Rose-Hulman-ROBO4xx/1314-BeagleBone-Quadcopter/code/ControlTower/images/BBB.jpg

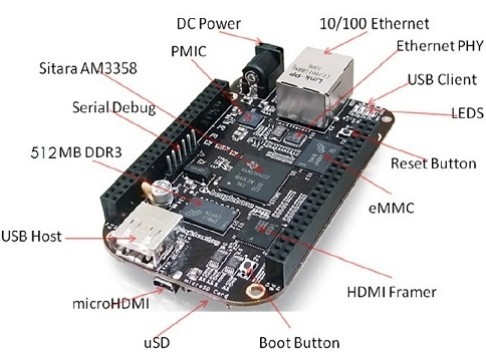
code/ControlTower/images/BBB.jpg
