Rose-Hulman-ROBO4xx/1314-BeagleBone-Quadcopter/code/ControlTower/images/Camera.jpg

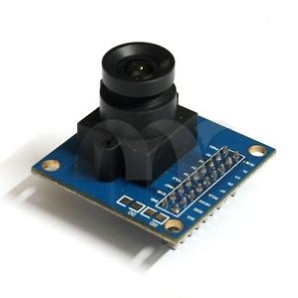
code/ControlTower/images/Camera.jpg
