Rose-Hulman-ROBO4xx/1314-BeagleBone-Quadcopter/code/ControlTower/images/Cape.jpg

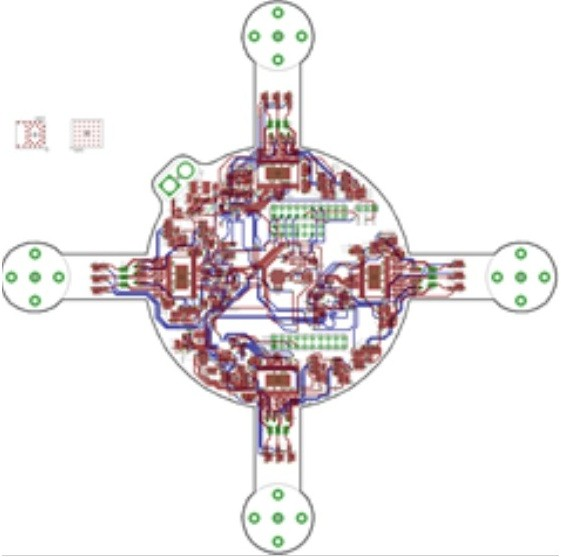
code/ControlTower/images/Cape.jpg
