Rose-Hulman-ROBO4xx/1314-BeagleBone-Quadcopter/code/ControlTower/images/forward_0.gif

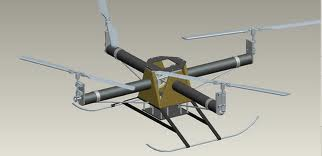
code/ControlTower/images/forward_0.gif
