Rose-Hulman-ROBO4xx/1314-BeagleBone-Quadcopter/code/ControlTower/images/forward_-1.gif

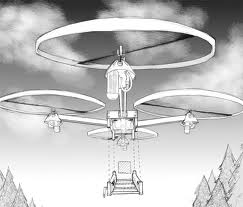
code/ControlTower/images/forward_-1.gif
