Rose-Hulman-ROBO4xx/1314-BeagleBone-Quadcopter/code/ControlTower/images/MPU.jpg

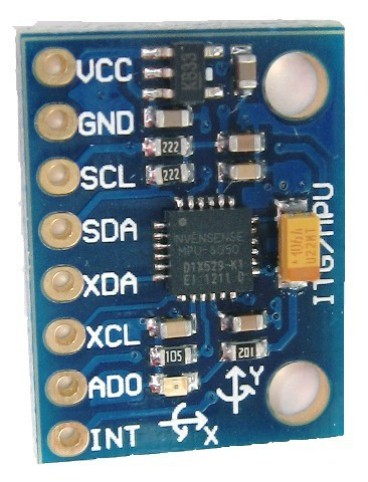
code/ControlTower/images/MPU.jpg
