Rose-Hulman-ROBO4xx/1314-BeagleBone-Quadcopter/code/ControlTower/images/original.gif

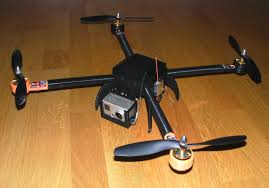
code/ControlTower/images/original.gif
