Rose-Hulman-ROBO4xx/1314-BeagleBone-Quadcopter/code/ControlTower/images/original.jpg

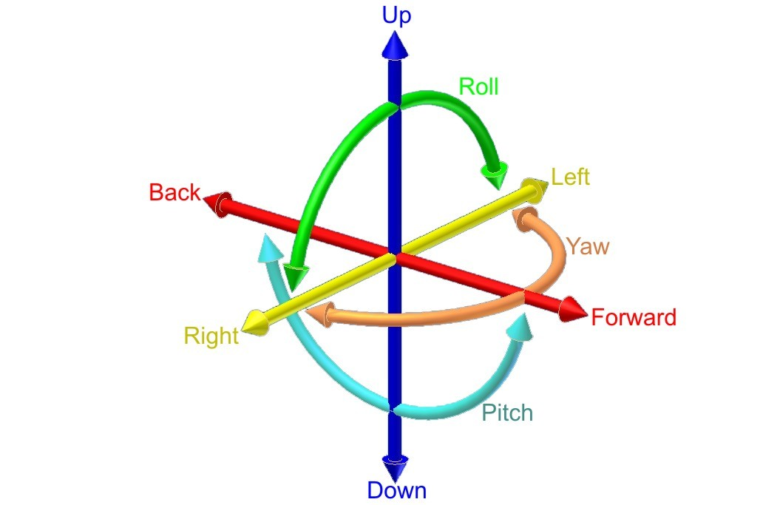
code/ControlTower/images/original.jpg
