Rose-Hulman-ROBO4xx/1314-BeagleBone-Quadcopter/code/ControlTower/images/QuadCopterImage.jpg

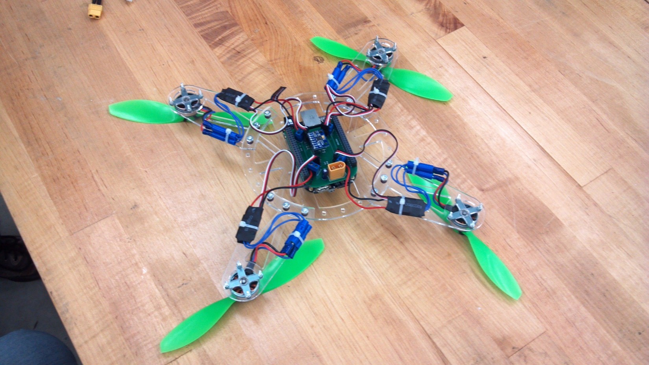
code/ControlTower/images/QuadCopterImage.jpg
