Rose-Hulman-ROBO4xx/1314-BeagleBone-Quadcopter/code/ControlTower/images/TIDog.png

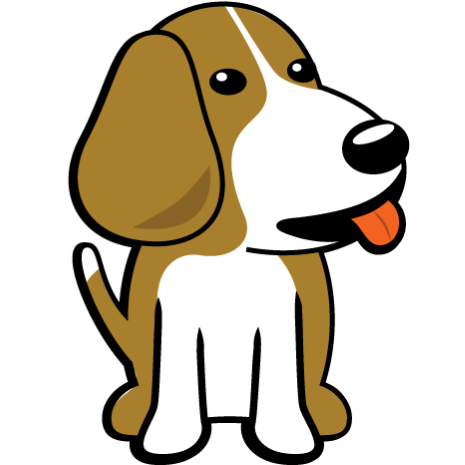
code/ControlTower/images/TIDog.png
