Rose-Hulman-ROBO4xx/1314-BeagleBone-Quadcopter/code/ControlTower/images/UltraSonic.jpg

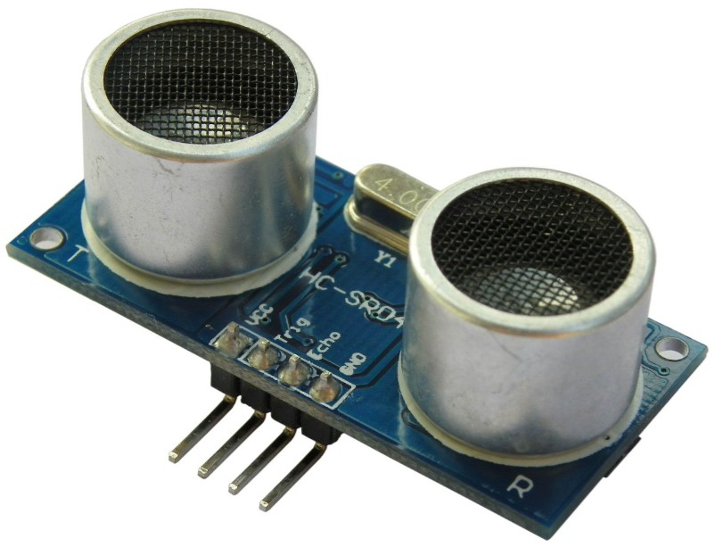
code/ControlTower/images/UltraSonic.jpg
