Rose-Hulman-ROBO4xx/1314-BeagleBone-Quadcopter/noncode/Board/Quad1brd.png

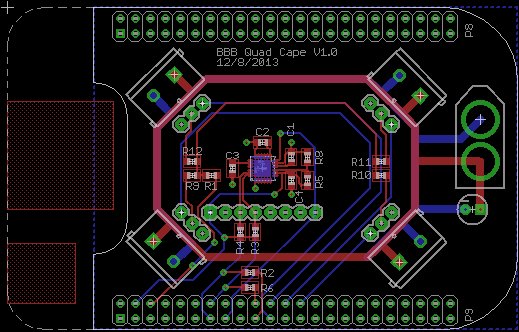
noncode/Board/Quad1brd.png
