Rose-Hulman-ROBO4xx/1314-BeagleBone-Quadcopter/noncode/Board/Quad2brd.png

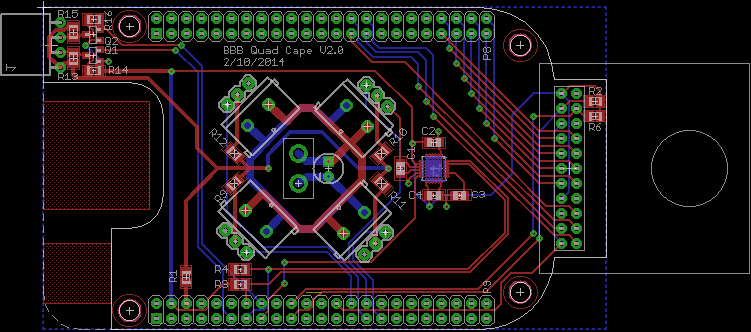
noncode/Board/Quad2brd.png
