Rose-Hulman-ROBO4xx/1314-BeagleBone-Quadcopter/noncode/Board/Quad3brd.png

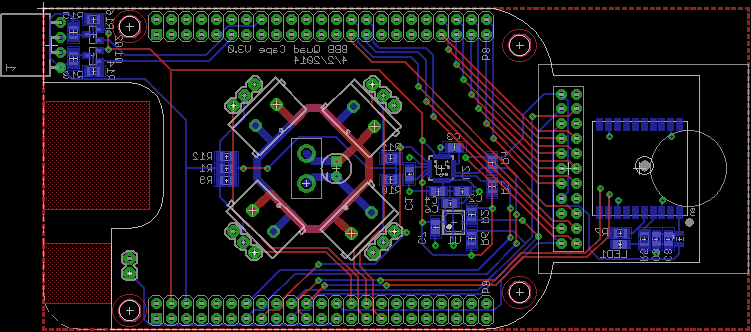
noncode/Board/Quad3brd.png
