Rose-Hulman-ROBO4xx/1314-BeagleBone-Quadcopter/noncode/Board/Quad32brd.png

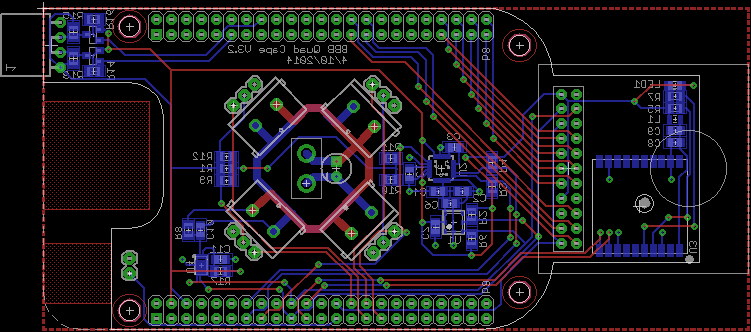
noncode/Board/Quad32brd.png
