Rose-Hulman-ROBO4xx/1314-BeagleBone-Quadcopter/noncode/Pictures/2013-12-18_14-34-24_871.jpg

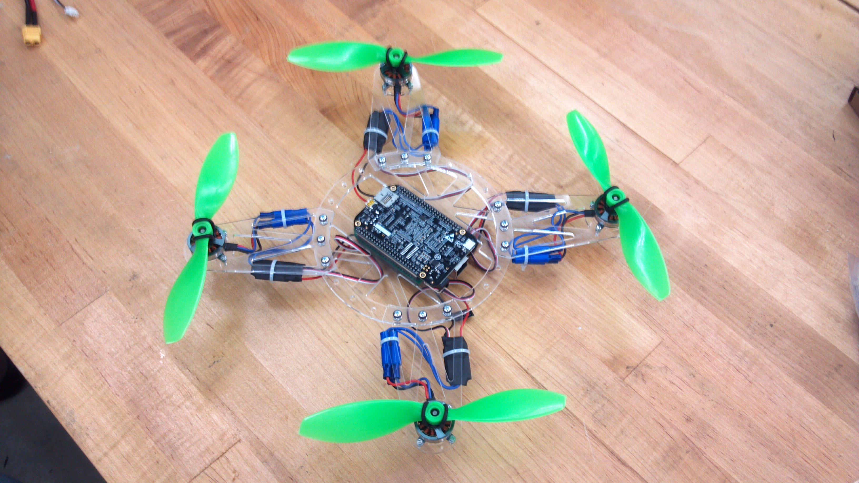
noncode/Pictures/2013-12-18_14-34-24_871.jpg
