Rose-Hulman-ROBO4xx/1314-BeagleBone-Quadcopter/noncode/CAD/Battery Tray 4.0 plywood tabbed.dxf

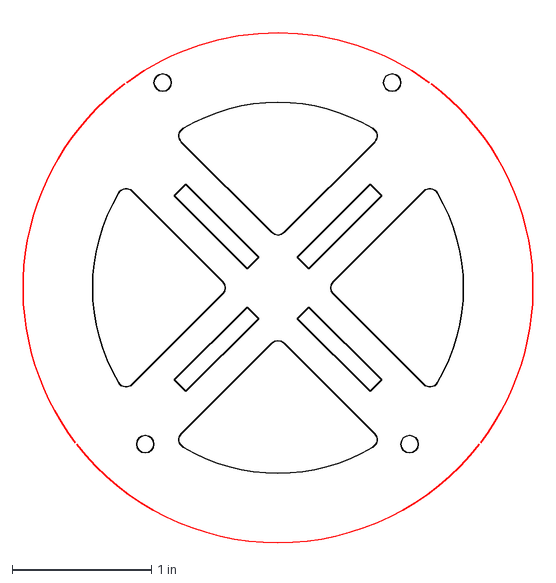
[picture p55: CAD file, 2014-04-13]
noncode/CAD/Battery Tray 4.0 plywood tabbed.dxf
3.77 x 3.79 in
