Rose-Hulman-ROBO4xx/1314-BeagleBone-Quadcopter/noncode/CAD/Layout 12x24 Plywood 4-7-14.dxf

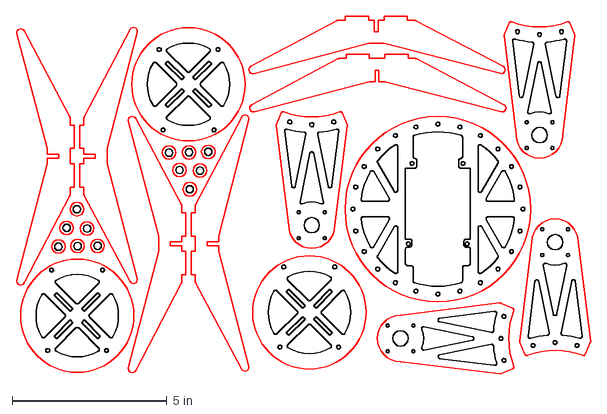
[picture p56: CAD file, 2014-04-13]
noncode/CAD/Layout 12x24 Plywood 4-7-14.dxf
18.6 x 11.6 in
