Rose-Hulman-ROBO4xx/1314-BeagleBone-Quadcopter/noncode/CAD/ESC.SLDPRT

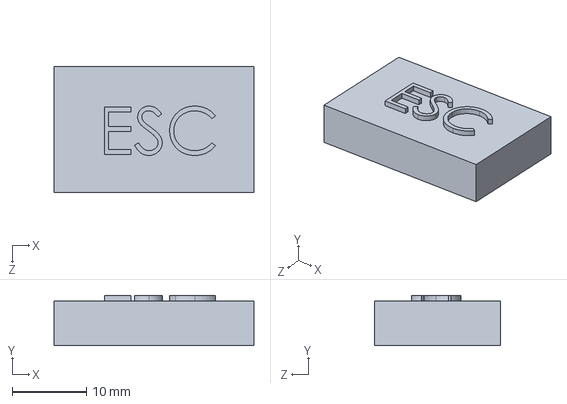
[picture p57: CAD file, 2014-04-13]
noncode/CAD/ESC.SLDPRT
27.0 x 6.76 x 17.0 mm
