Rose-Hulman-ROBO4xx/1314-BeagleBone-Quadcopter/noncode/CAD/Layout 12x12 with Grain.dxf

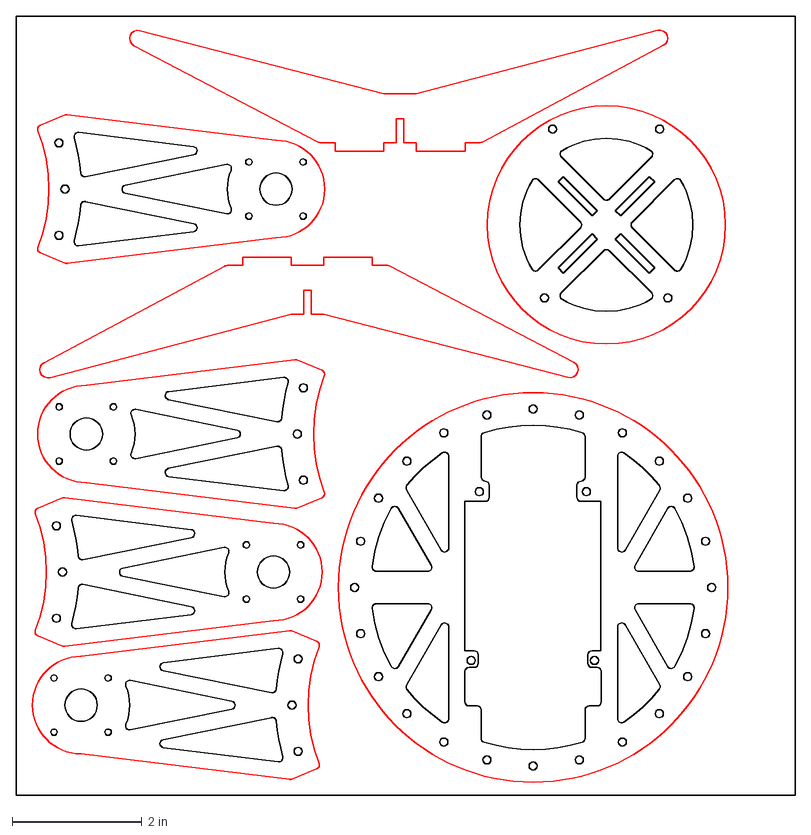
[picture p59: CAD file, 2014-04-13]
noncode/CAD/Layout 12x12 with Grain.dxf
12.0 x 12.0 in
