Rose-Hulman-ROBO4xx/1314-BeagleBone-Quadcopter/noncode/CAD/Battery Tray 4.0 plywood.dxf

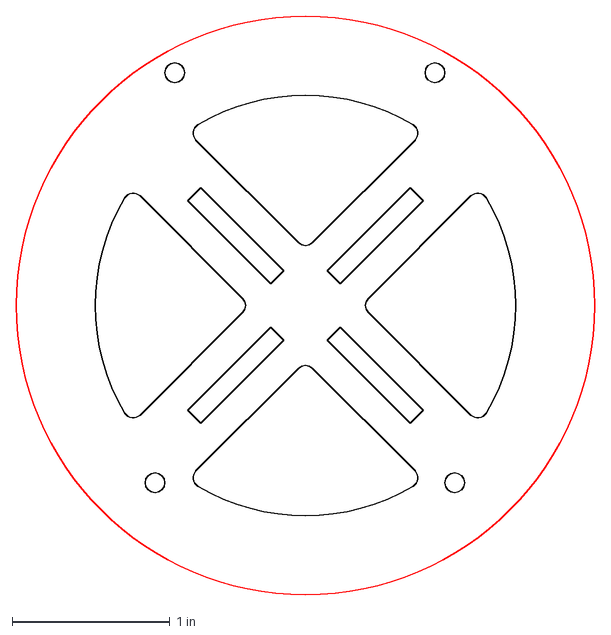
[picture p60: CAD file, 2014-04-13]
noncode/CAD/Battery Tray 4.0 plywood.dxf
3.67 x 3.67 in
