Rose-Hulman-ROBO4xx/1314-BeagleBone-Quadcopter/noncode/CAD/Battery Tray 4.0.SLDPRT

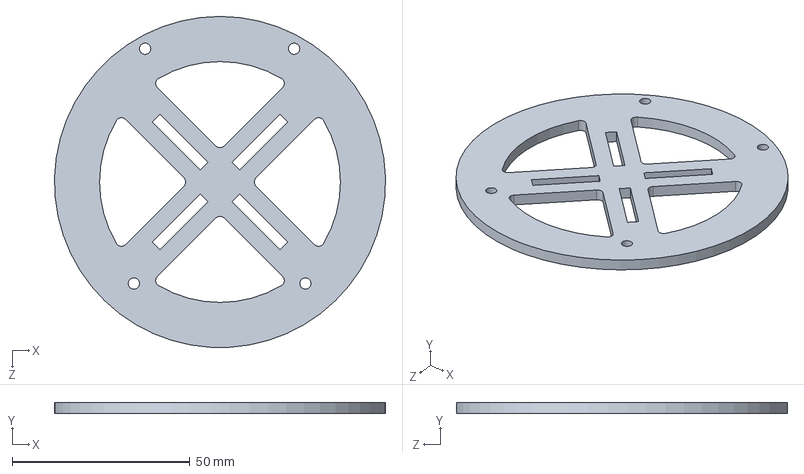
[picture p61: CAD file, 2014-04-13]
noncode/CAD/Battery Tray 4.0.SLDPRT
93.1 x 3.17 x 93.2 mm
