Rose-Hulman-ROBO4xx/1314-BeagleBone-Quadcopter/noncode/CAD/Arm 4.0.SLDPRT

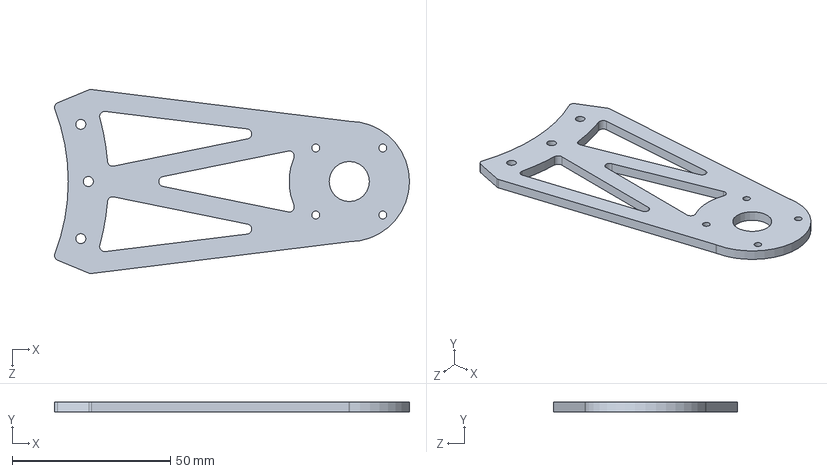
[picture p62: CAD file, 2014-04-13]
noncode/CAD/Arm 4.0.SLDPRT
112.3 x 3.17 x 58.2 mm
