Rose-Hulman-ROBO4xx/1314-BeagleBone-Quadcopter/noncode/CAD/Propellor.SLDPRT

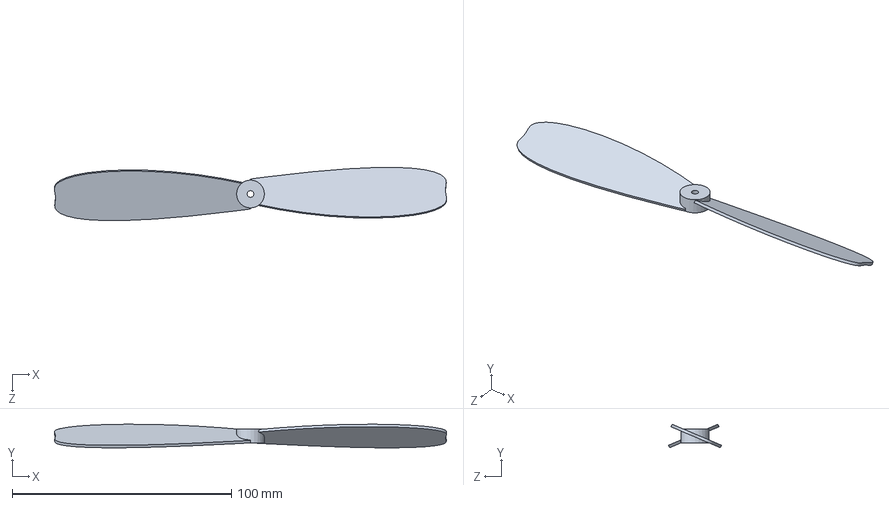
[picture p63: CAD file, 2014-04-13]
noncode/CAD/Propellor.SLDPRT
178.8 x 10.8 x 24.2 mm
