Rose-Hulman-ROBO4xx/1314-BeagleBone-Quadcopter/noncode/CAD/Leg2 4.0 solid plywood.dxf

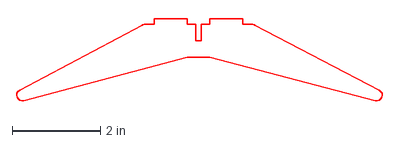
[picture p64: CAD file, 2014-04-13]
noncode/CAD/Leg2 4.0 solid plywood.dxf
8.32 x 1.87 in
