Rose-Hulman-ROBO4xx/1314-BeagleBone-Quadcopter/noncode/CAD/Frame 4.0.SLDPRT

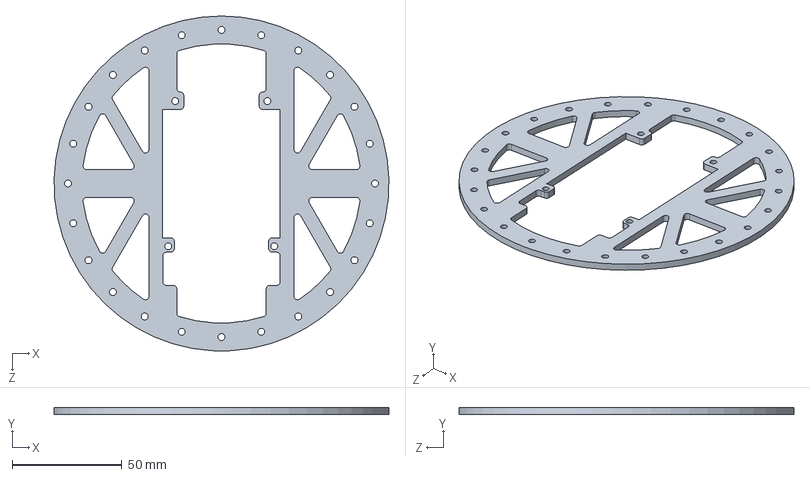
[picture p65: CAD file, 2014-04-13]
noncode/CAD/Frame 4.0.SLDPRT
152.3 x 3.17 x 152.4 mm
