Rose-Hulman-ROBO4xx/1314-BeagleBone-Quadcopter/noncode/CAD/Leg1 4.0 solid plywood.dxf

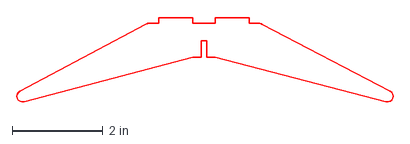
[picture p66: CAD file, 2014-04-13]
noncode/CAD/Leg1 4.0 solid plywood.dxf
8.32 x 1.87 in
