Rose-Hulman-ROBO4xx/1314-BeagleBone-Quadcopter/noncode/CAD/Leg2 4.0 solid plywood tabbed.dxf

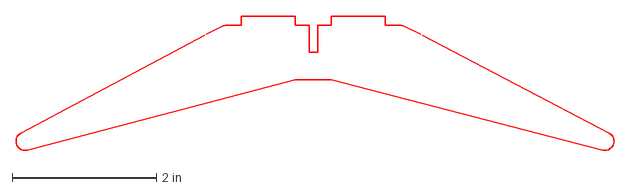
[picture p67: CAD file, 2014-04-13]
noncode/CAD/Leg2 4.0 solid plywood tabbed.dxf
8.29 x 1.87 in
