Rose-Hulman-ROBO4xx/1314-BeagleBone-Quadcopter/noncode/CAD/Prototype 3.SLDPRT

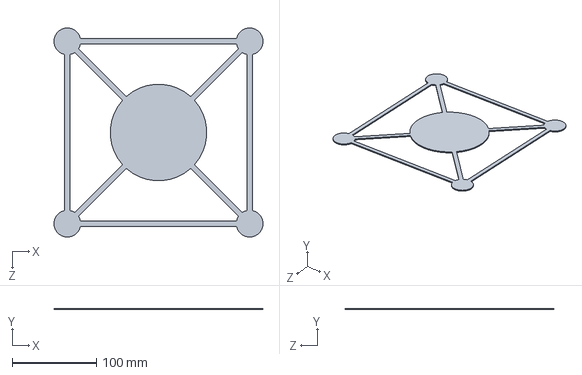
[picture p68: CAD file, 2014-04-08]
noncode/CAD/Prototype 3.SLDPRT
247.5 x 1.57 x 247.5 mm
