Rose-Hulman-ROBO4xx/1314-BeagleBone-Quadcopter/noncode/CAD/Battery 1.0.SLDPRT

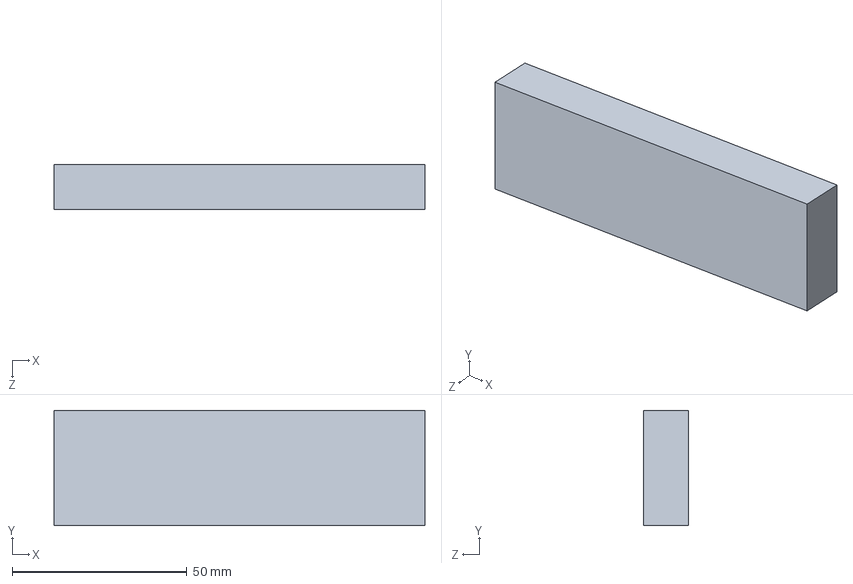
[picture p69: CAD file, 2014-04-08]
noncode/CAD/Battery 1.0.SLDPRT
106.0 x 33.0 x 13.0 mm
