Rose-Hulman-ROBO4xx/1314-BeagleBone-Quadcopter/noncode/CAD/Frame 1.0.SLDPRT

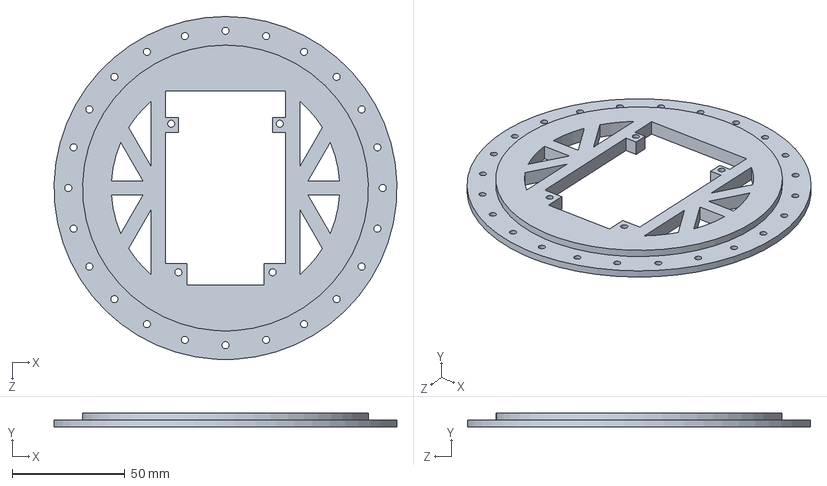
[picture p71: CAD file, 2014-04-08]
noncode/CAD/Frame 1.0.SLDPRT
152.3 x 6.35 x 152.4 mm
