Rose-Hulman-ROBO4xx/1314-BeagleBone-Quadcopter/noncode/CAD/Arm 2.0.SLDPRT

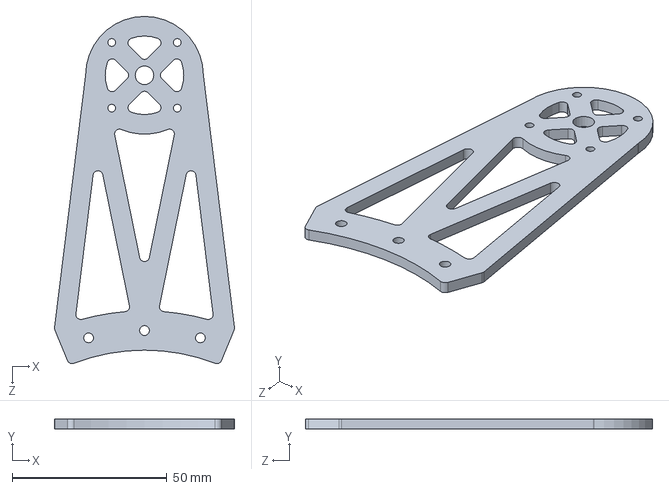
[picture p72: CAD file, 2014-04-08]
noncode/CAD/Arm 2.0.SLDPRT
58.2 x 3.17 x 112.3 mm
