Rose-Hulman-ROBO4xx/1314-BeagleBone-Quadcopter/noncode/CAD/Battery Tray 1.0.SLDPRT

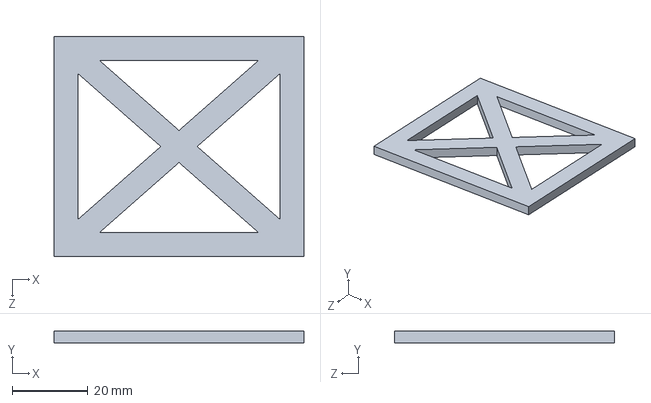
[picture p73: CAD file, 2014-04-08]
noncode/CAD/Battery Tray 1.0.SLDPRT
66.0 x 3.17 x 58.1 mm
