Rose-Hulman-ROBO4xx/1314-BeagleBone-Quadcopter/noncode/CAD/Leg2 2.0.SLDPRT

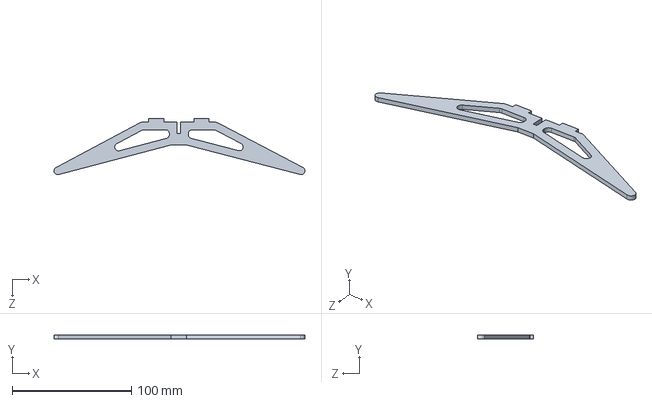
[picture p75: CAD file, 2014-04-08]
noncode/CAD/Leg2 2.0.SLDPRT
210.5 x 3.17 x 47.2 mm
