Rose-Hulman-ROBO4xx/1314-BeagleBone-Quadcopter/noncode/CAD/Leg2 1.0.SLDPRT

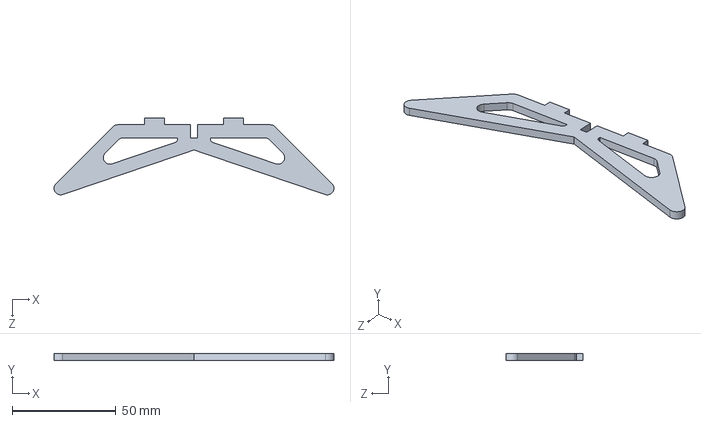
[picture p76: CAD file, 2014-04-08]
noncode/CAD/Leg2 1.0.SLDPRT
134.8 x 3.17 x 37.0 mm
