Rose-Hulman-ROBO4xx/1314-BeagleBone-Quadcopter/noncode/CAD/Layout LegSpacer 4-7-14.dxf

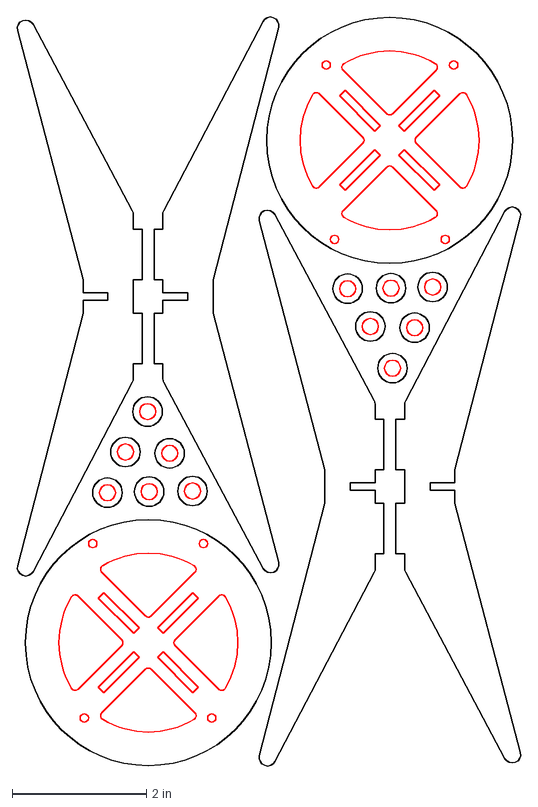
[picture p77: CAD file, 2014-04-08]
noncode/CAD/Layout LegSpacer 4-7-14.dxf
7.53 x 11.2 in
