Rose-Hulman-ROBO4xx/1314-BeagleBone-Quadcopter/noncode/CAD/Arm 1.0.SLDPRT

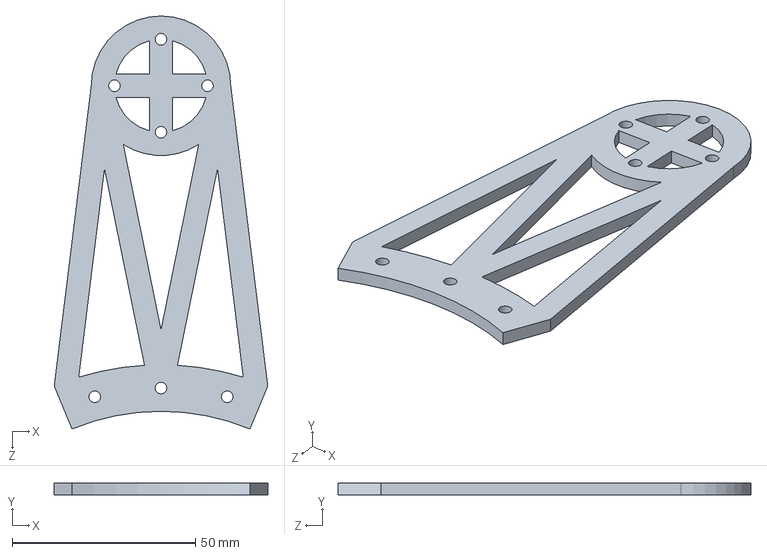
[picture p79: CAD file, 2014-04-08]
noncode/CAD/Arm 1.0.SLDPRT
58.3 x 3.17 x 112.8 mm
