Rose-Hulman-ROBO4xx/1314-BeagleBone-Quadcopter/noncode/CAD/Layout 12x12.dxf

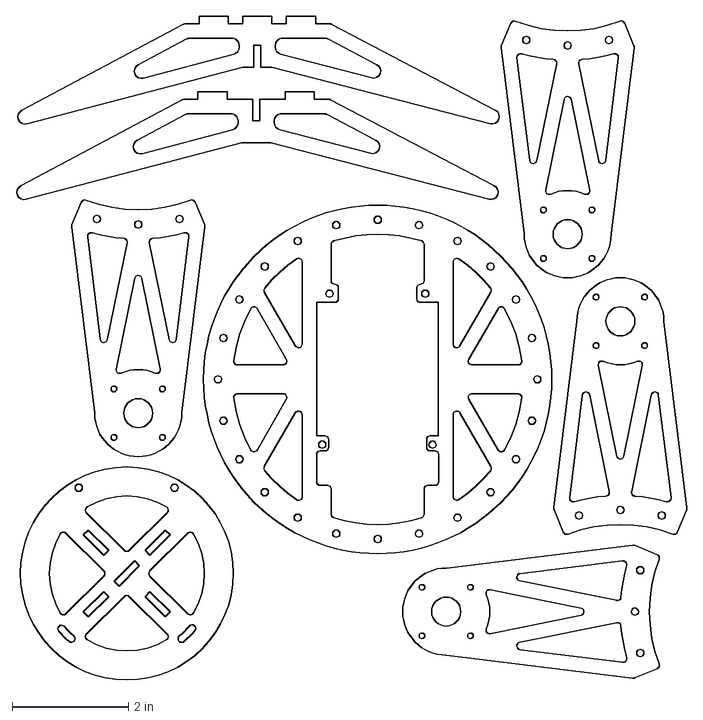
[picture p80: CAD file, 2014-04-08]
noncode/CAD/Layout 12x12.dxf
11.6 x 11.4 in
