Rose-Hulman-ROBO4xx/1314-BeagleBone-Quadcopter/noncode/CAD/Leg2 4.0 solid.dxf

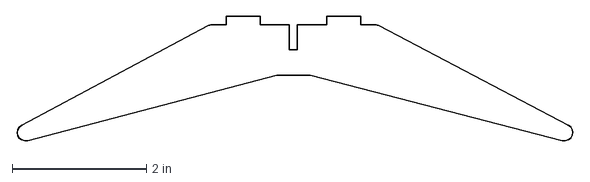
[picture p81: CAD file, 2014-04-08]
noncode/CAD/Leg2 4.0 solid.dxf
8.32 x 1.87 in
