Rose-Hulman-ROBO4xx/1314-BeagleBone-Quadcopter/noncode/CAD/Battery Tray 1.5.SLDPRT

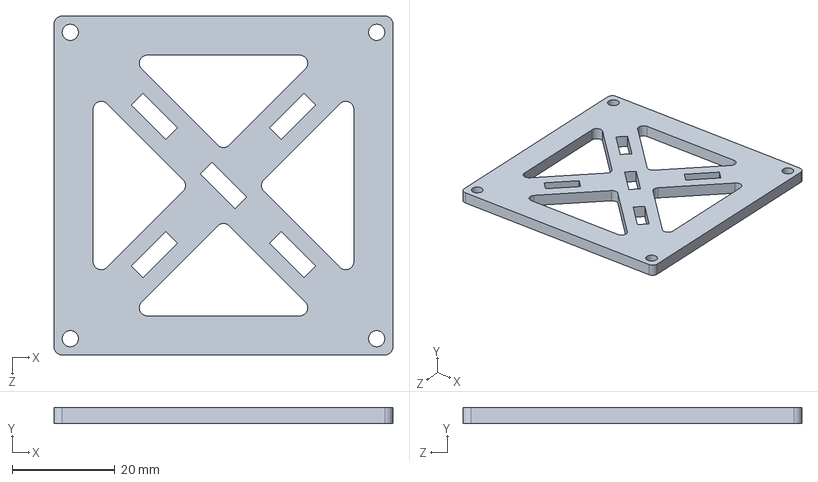
[picture p82: CAD file, 2014-04-08]
noncode/CAD/Battery Tray 1.5.SLDPRT
66.0 x 3.17 x 66.0 mm
