Rose-Hulman-ROBO4xx/1314-BeagleBone-Quadcopter/noncode/CAD/Standoff 1.0.SLDPRT

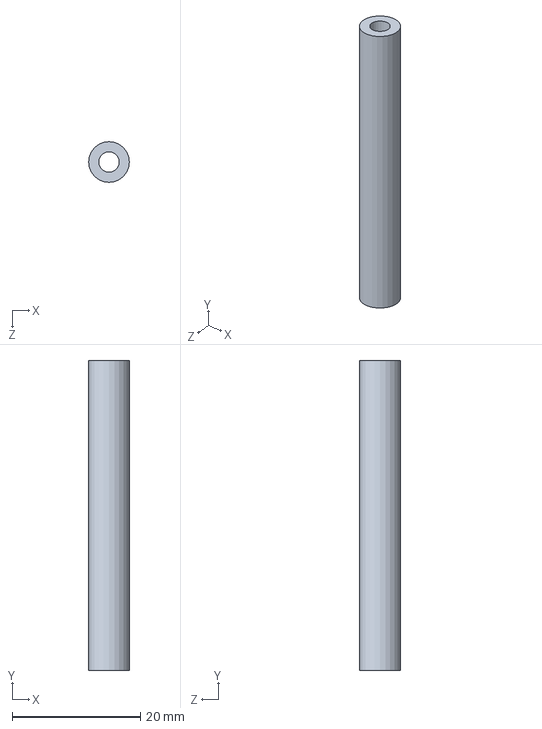
[picture p83: CAD file, 2014-04-08]
noncode/CAD/Standoff 1.0.SLDPRT
6.35 x 48.3 x 6.35 mm
