Rose-Hulman-ROBO4xx/1314-BeagleBone-Quadcopter/noncode/CAD/BEAGLEBONE_BLACK_BOARD.SLDPRT

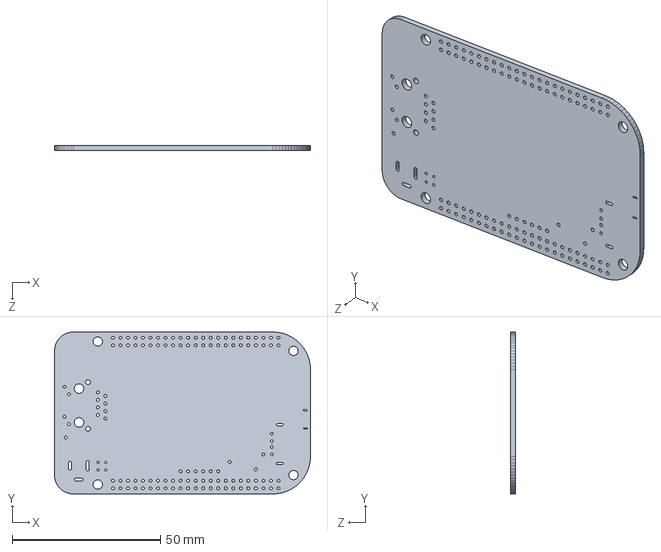
[picture p84: CAD file, 2014-04-08]
noncode/CAD/BEAGLEBONE_BLACK_BOARD.SLDPRT
86.4 x 54.7 x 1.57 mm
